govido/iVAM8/Printed parts STLs/Y-axis/y-tensioner.stl

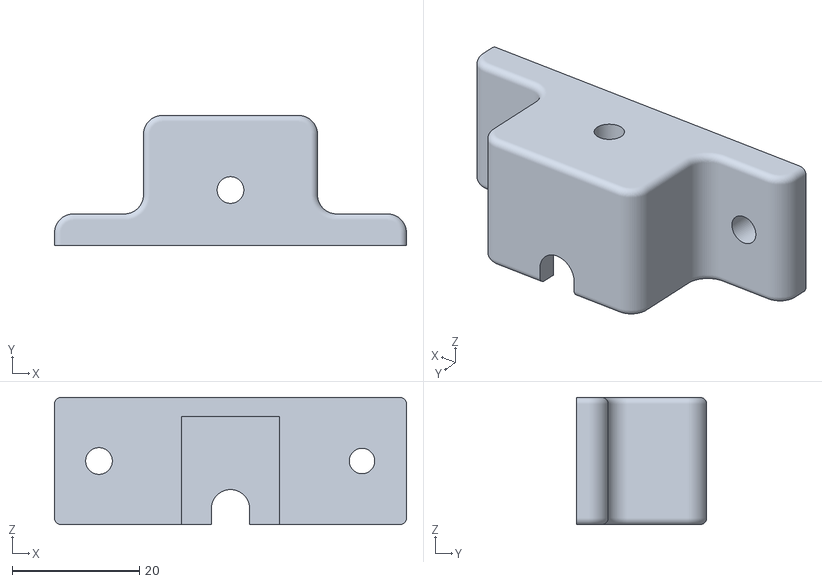
[picture p17: CAD file, 2022-01-15]
Printed parts STLs/Y-axis/y-tensioner.stl
55.4 x 20.5 x 20.0
