govido/iVAM8/Printed parts STLs/Y-axis/lm8uu_slim+.stl

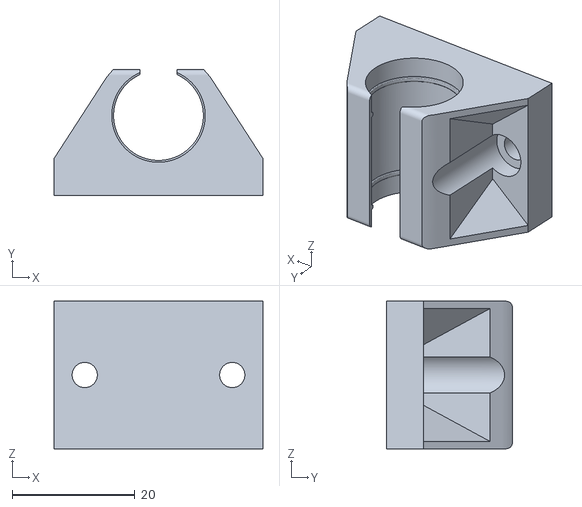
[picture p18: CAD file, 2022-01-15]
Printed parts STLs/Y-axis/lm8uu_slim+.stl
34.0 x 20.5 x 24.0
