govido/iVAM8/Printed parts STLs/Y-axis/y-idler.stl

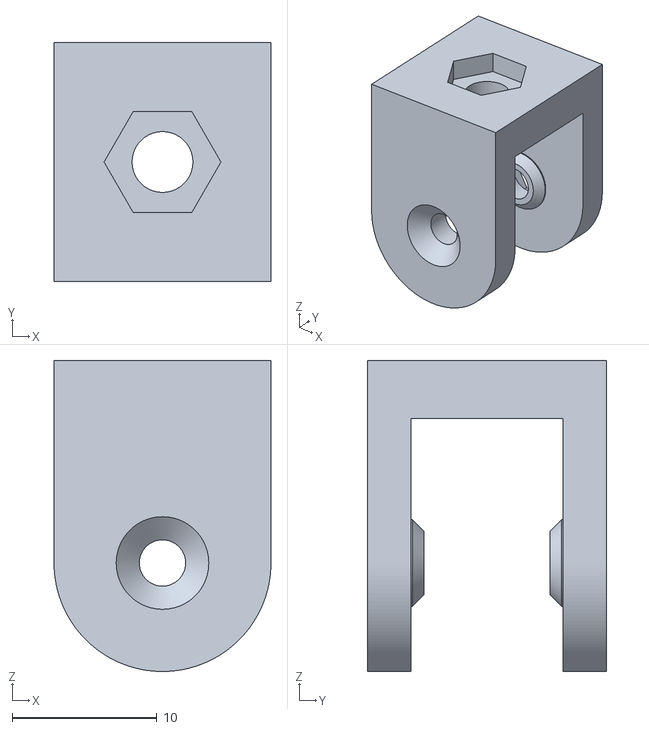
[picture p19: CAD file, 2022-01-15]
Printed parts STLs/Y-axis/y-idler.stl
15.0 x 16.5 x 21.5
