govido/iVAM8/Printed parts STLs/Electronics/PSU-left.stl

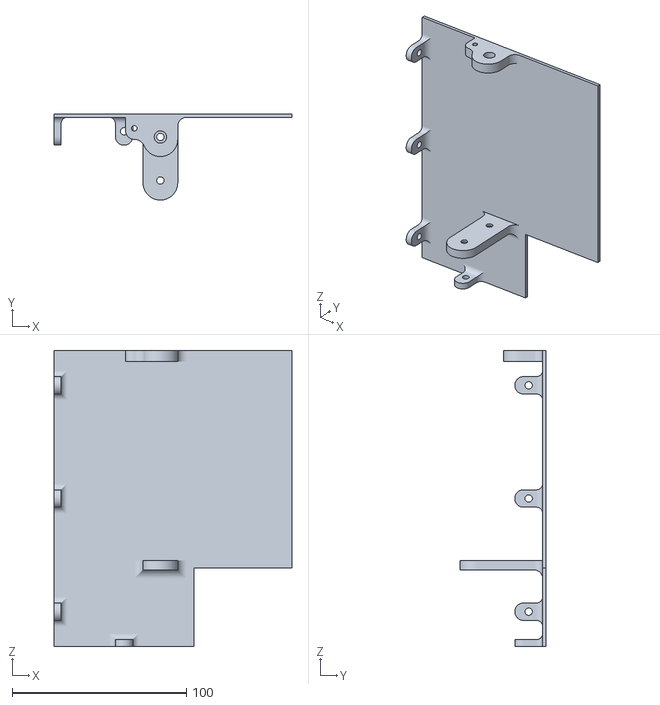
[picture p20: CAD file, 2022-01-15]
Printed parts STLs/Electronics/PSU-left.stl
136.5 x 49.5 x 170.0
