govido/iVAM8/Printed parts STLs/Y-axis/Y-Stepper-mount.stl

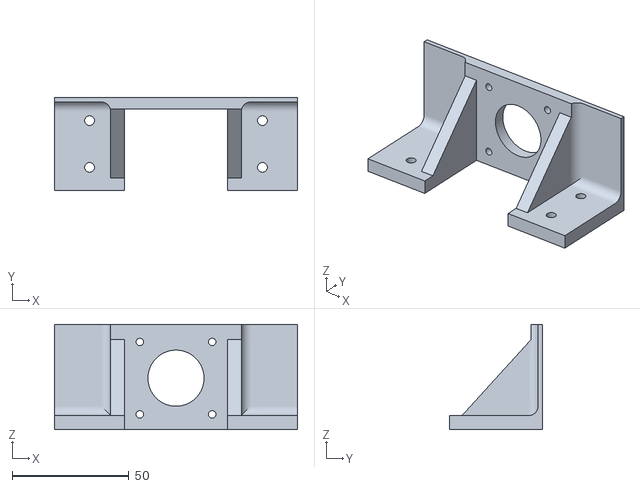
[picture p21: CAD file, 2022-01-15]
Printed parts STLs/Y-axis/Y-Stepper-mount.stl
104.0 x 40.0 x 45.0
