govido/iVAM8/Printed parts STLs/Electronics/V2_skr gtr_2.stl

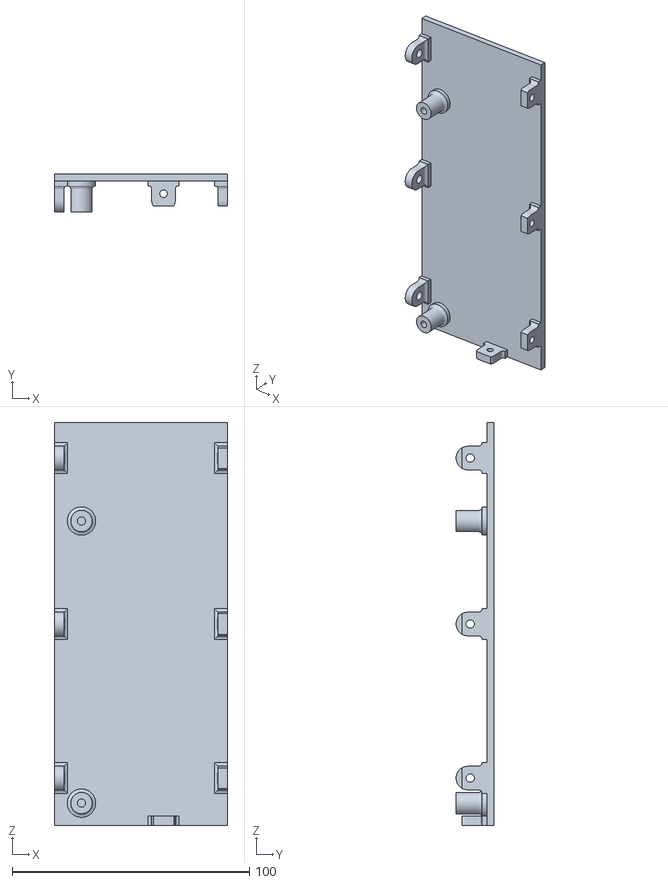
[picture p22: CAD file, 2022-01-15]
Printed parts STLs/Electronics/V2_skr gtr_2.stl
73.0 x 16.0 x 170.0
