govido/iVAM8/Printed parts STLs/Electronics/V2_skr gtr_1.stl

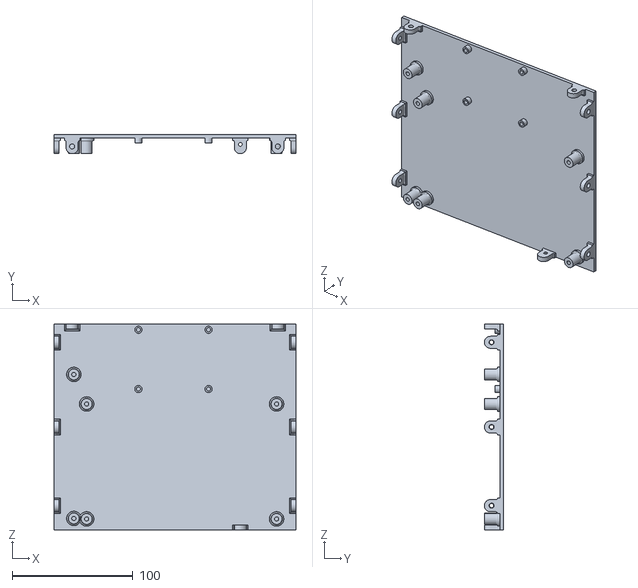
[picture p23: CAD file, 2022-01-15]
Printed parts STLs/Electronics/V2_skr gtr_1.stl
200.0 x 16.0 x 170.0
