govido/iVAM8/Printed parts STLs/Electronics/PSU-right.stl

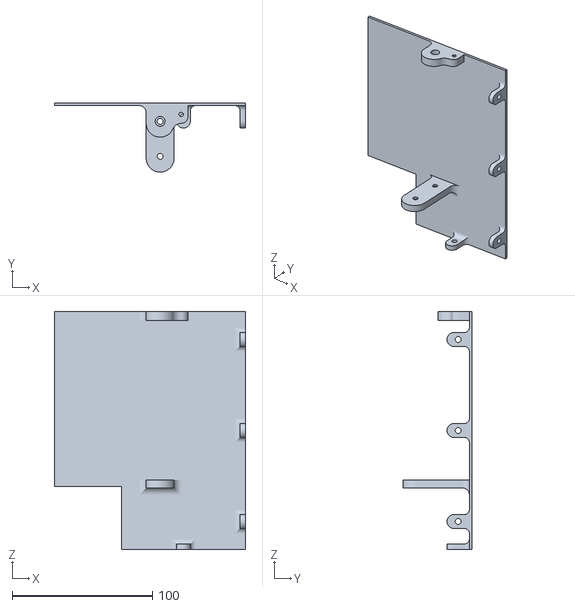
[picture p24: CAD file, 2022-01-15]
Printed parts STLs/Electronics/PSU-right.stl
136.5 x 49.5 x 170.0
