govido/iVAM8/Klipper config/T0-SB2040.cfg

## SB2040 BOARD PINS
[board_pins T0-SB2040]
mcu: T0-SB2040
aliases:
aliases_2209:
    EXT_EN=gpio7,EXT_STEP=gpio9,EXT_DIR=gpio10,EXT_UART=gpio8
aliases_endstop:
    LIMIT_0=gpio25,LIMIT_1=gpio28,LIMIT_2=gpio29
aliases_cnc_fans:
    FAN0=gpio13,FAN1=gpio14,FAN2=gpio15
aliases_thermistors:
    TH0=gpio27,TH1=gpio26
aliases_heaters:
    HE0=gpio6
aliases_rgb:
    RGBLED=gpio12
aliases_adxl:
    ADXL=gpio1

[mcu T0-SB2040]
canbus_uuid: d7f85712e8d5   #87cbb18ca617

[temperature_sensor T0-SB2040]
sensor_type: temperature_mcu
sensor_mcu: T0-SB2040

[temperature_sensor T0-Ambient]
sensor_type: EPCOS 100K B57560G104F
sensor_pin: T0-SB2040:TH1

[heater_fan hotend0_fan]
pin: T0-SB2040:FAN1
max_power: 0.75
kick_start_time: 0.5
heater: extruder
heater_temp: 50.0
shutdown_speed: 0

[fan]
pin: rpi:gpio20

[fan_generic fan_extruder]
pin: T0-SB2040:FAN0
kick_start_time: 1.00
cycle_time: 0.15
off_below: 0.10

[extruder]
step_pin: T0-SB2040:EXT_STEP
dir_pin: T0-SB2040:EXT_DIR
enable_pin: !T0-SB2040:EXT_EN
rotation_distance: 22.67895 # VZHextrudort, Mini SHerpa and other BMG based extruders
gear_ratio: 50:10 
microsteps: 16
full_steps_per_rotation: 200
max_extrude_only_distance: 1000.0
max_extrude_only_velocity: 50.0
max_extrude_only_accel: 1500
nozzle_diameter: 0.400
filament_diameter: 1.750
heater_pin: T0-SB2040:HE0
sensor_pin: T0-SB2040:TH0
sensor_type: EPCOS 100K B57560G104F  # this is the default for the Revo heater
#pullup_resistor: 2200             # Uncomment for PT100 Sensor with jumper installed. 
control = pid
pid_Kp=17.357 
pid_Ki=0.629 
pid_Kd=119.760
min_temp: 0
max_temp: 275
min_extrude_temp: 160

[tmc2209 extruder]
uart_pin: T0-SB2040:EXT_UART
stealthchop_threshold: 0
run_current: 0.32

[adxl345 t0]
cs_pin: T0-SB2040:ADXL
spi_software_sclk_pin: T0-SB2040:gpio0
spi_software_mosi_pin: T0-SB2040:gpio3
spi_software_miso_pin: T0-SB2040:gpio2

[bltouch]
sensor_pin: ^T0-SB2040:gpio29
control_pin: T0-SB2040:gpio28
x_offset: 0
y_offset: 20.5
#z_offset: 1.78
pin_up_touch_mode_reports_triggered: False
